andreibalica/Proiect---InkTime/Images/PCB_TOP.png

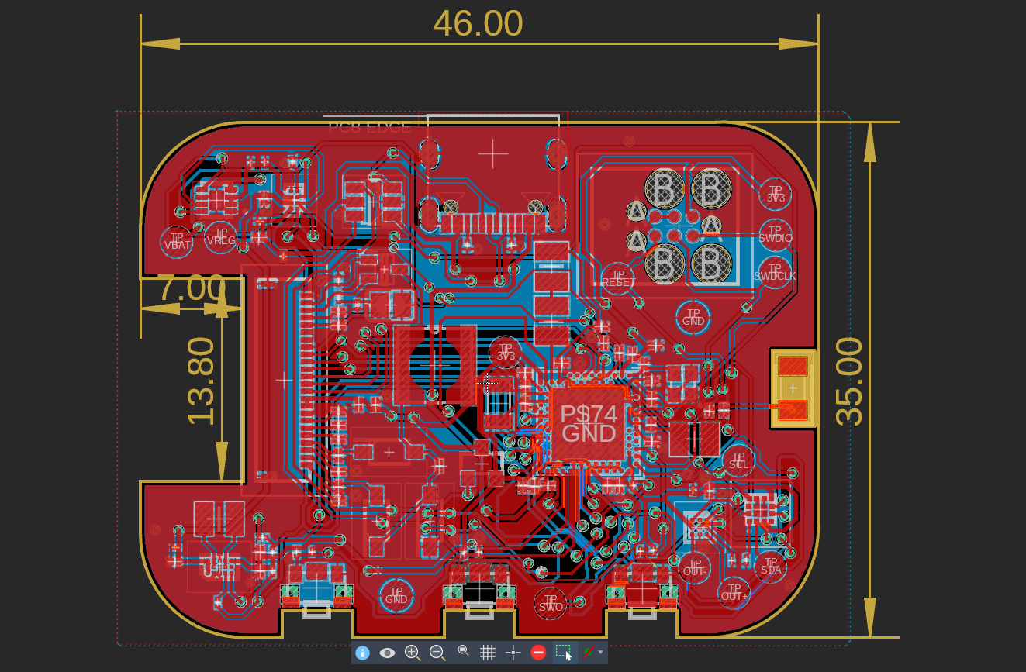
Images/PCB_TOP.png
